Siromanec/video-scrambler/FPGA/core/src/sequence_management/rtl/sequence_generator_switch.v

module sequence_generator_switch (
   input wire clk,
   input wire reset_n,
   input wire H,
   input wire V,
   input wire [9:0] bt656_stream_in,
   input wire [9:0] sequence_in,
   output wire [9:0] bt656_stream_out,
   output wire V_out,
   output reg enable_generator,
   output reg load_generator
);
   localparam ACTIVE_VIDEO_PIXELS = 2 * 720;
   reg prev_V, prev_H;
   wire V_fall = prev_V && !V;
   wire H_fall = prev_H && !H;
   wire V_rise = !prev_V && V;
   wire H_rise = !prev_H && H;

   reg  V_internal;
   // does not actually change the vsync in the stream, it is a trick for line rotator to not do encryption
   assign V_out = V || V_internal;

   reg [$clog2(ACTIVE_VIDEO_PIXELS)-1:0] pixel_cnt;
   reg allow_counter;
   reg allow_out;
   reg sequence_done;
   assign bt656_stream_out = allow_out ? sequence_in : bt656_stream_in;

   // // V V_lag V_out
   // // 0   0   0
   // // 0   1   1
   // // 1   0   1
   // // 1   1   1
   // reg V_lag1;
   // reg V_soften;
   // for some reason modelsim generates zero-tick low pulse for the output of V_out 
   // when V changes state which is enough to break everything

   // always @(posedge H or negedge reset_n) begin
   //    if (!reset_n) begin
   //       V_lag1 <= V;
   //       V_out <= V;
   //    end else begin
   //       V_out <= V_soften | V | V_lag1; 
   //       V_lag1 <= V;
   //    end
   // end

   always @(posedge clk or negedge reset_n) begin
      if (!reset_n) begin
         prev_V <= 0;
         prev_H <= 0;
         V_internal <= 0;

         pixel_cnt <= 0;
         allow_out <= 0;
         allow_counter <= 0;
         sequence_done <= 0;

         load_generator <= 0;
         enable_generator <= 0;
         
      end else begin

         prev_V <= V;
         prev_H <= H;

         if (V) begin
            V_internal <= 1;
            sequence_done <= 0;
         end else if (V_fall) begin
            load_generator   <= 1;
            enable_generator <= 1;
         end else if (H_fall && !sequence_done) begin
            load_generator <= 0;
            allow_counter <= 1;
            allow_out <= 1;
            pixel_cnt <= 0;
         end else if (!H && allow_counter) begin
            if (pixel_cnt < ACTIVE_VIDEO_PIXELS - 3) begin
               pixel_cnt <= pixel_cnt + 1;
            end else begin
               allow_out <= 0;
               enable_generator <= 0;
               sequence_done <= 1;
               V_internal <= 0;
               allow_counter <= 0;
            end 
         end
      end
   end
endmodule
